schwicke/hexapod-robi/media/20210815_222941.jpg

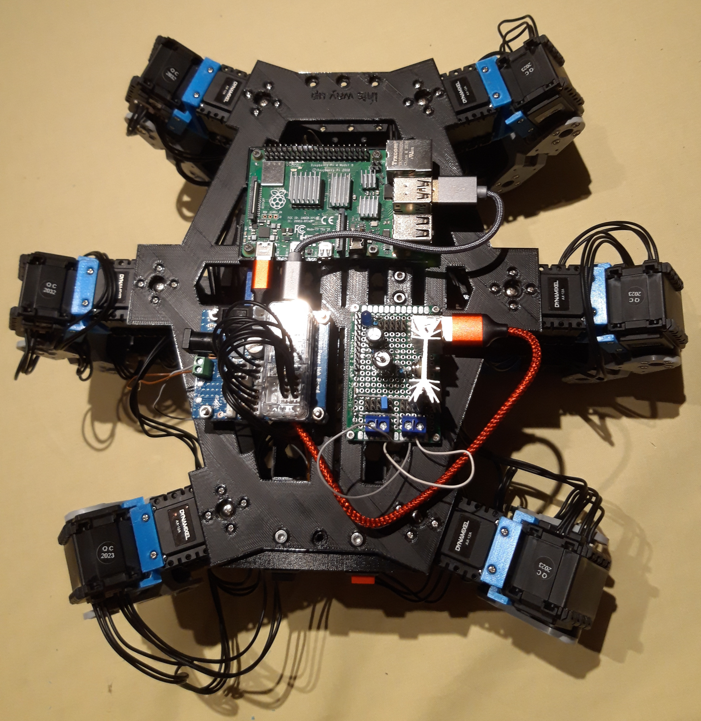
media/20210815_222941.jpg
