schwicke/hexapod-robi/hardware/scad/body/bodymiddle.scad

//
// This file is part of the hexapod-robi distribution (https://github.com/schwicke/hexapod-robi).
// Copyright (c) 2021 Ulrich Schwickerath
//
// This program is free software: you can redistribute it and/or modify
// it under the terms of the GNU General Public License as published by
// the Free Software Foundation, version 3.
//
// This program is distributed in the hope that it will be useful, but
// WITHOUT ANY WARRANTY; without even the implied warranty of
// MERCHANTABILITY or FITNESS FOR A PARTICULAR PURPOSE. See the GNU
// General Public License for more details.
//
// You should have received a copy of the GNU General Public License
// along with this program. If not, see <http://www.gnu.org/licenses/>.
//
// This is a little plastic bit which is intended to get the holes for the connectors
// at the right position. It's not part of the robot itself, but useful for building it.
//

include <../lib/globals.scad>
include <../lib/nuts_and_screws.scad>
include <../lib/mounts.scad>
include <../lib/bodyhelpers.scad>

// global parameters
top_size_scaler = 0.8;

// electronics
power_pos_x = 25;
power_pos_y = 58;
power_spacer_height = 3;
power_converter_scale = 0.7;
//
pcb_hole_dist = 2.0;
pcb_spacer_height = 3;
pcb_x_size = 40;
pcb_y_size = 60;

// disk
delta = 0.2;
ssd_x = 75.0 + delta;
ssd_y = 57.0 + delta;
ssd_z = 11.0 + delta;
ssd_pos_x = 0;
ssd_pos_y = -50;
ssd_height = ssd_z + thickness;
module pcb_spacers(x, y, d, mode){
     // spacers
     translate([-power_pos_x, power_pos_y, 0]){
          translate([ x/2-pcb_hole_dist,  y/2-pcb_hole_dist, 0])spacer_mX(d, pcb_spacer_height);
          translate([ x/2-pcb_hole_dist, -y/2+pcb_hole_dist, 0])spacer_mX(d, pcb_spacer_height);
          translate([-x/2+pcb_hole_dist,  y/2-pcb_hole_dist, 0])spacer_mX(d, pcb_spacer_height);
          translate([-x/2+pcb_hole_dist, -y/2+pcb_hole_dist, 0])spacer_mX(d, pcb_spacer_height);
     }
}

module pcb_holes(x, y, d, mode){
     translate([-power_pos_x, power_pos_y, 0]){
          translate([ x/2-pcb_hole_dist,  y/2-pcb_hole_dist, 0])if (mode==0) my_screwhole_mX(d); else nuthole_mX(d);
          translate([ x/2-pcb_hole_dist, -y/2+pcb_hole_dist, 0])if (mode==0) my_screwhole_mX(d); else nuthole_mX(d);
          translate([-x/2+pcb_hole_dist,  y/2-pcb_hole_dist, 0])if (mode==0) my_screwhole_mX(d); else nuthole_mX(d);
          translate([-x/2+pcb_hole_dist, -y/2+pcb_hole_dist, 0])if (mode==0) my_screwhole_mX(d); else nuthole_mX(d);
     }
}

module power_spacers(scale, d, mode){
  // add spacers
  translate([power_pos_x, power_pos_y, 0]){
    translate([ 24*scale, 21*scale, 0])spacer_mX(d, power_spacer_height);
    translate([-24*scale, 21*scale, 0])spacer_mX(d, power_spacer_height);
    translate([ 24*scale,-21*scale, 0])spacer_mX(d, power_spacer_height);
    translate([-24*scale,-21*scale, 0])spacer_mX(d, power_spacer_height);
  }
}

module power_holes(scale, d, mode){
  translate([power_pos_x, power_pos_y, 0])
    union(){
    translate([ 24*scale, 21*scale, 0]) rotate([0,180,0]) if (mode==0) my_screwhole_mX(d); else nuthole_mX(d);
    translate([-24*scale, 21*scale, 0]) rotate([0,180,0]) if (mode==0) my_screwhole_mX(d); else nuthole_mX(d);
    translate([ 24*scale,-21*scale, 0]) rotate([0,180,0]) if (mode==0) my_screwhole_mX(d); else nuthole_mX(d);
    translate([-24*scale,-21*scale, 0]) rotate([0,180,0]) if (mode==0) my_screwhole_mX(d); else nuthole_mX(d);
  }
}

module ssd_frame(){
     difference(){
          cube([ssd_x+thickness+0.1, ssd_y+thickness+0.1, ssd_height], center=true);
          translate([0, 0, thickness])cube([ssd_x, ssd_y, ssd_height], center=true);
          translate([ssd_x/2, 0, thickness])cube([40, 40, ssd_height], center=true);
          translate([-ssd_x/2, 0, thickness])cube([40, 40, ssd_height], center=true);
     }
}

module mount(){
  //translate([0., 0., space/2  ])cube([10, 20, space+thickness/2], center=true);
  wx = 4*raster+raster/2;
  wy = 8*raster+raster/2;
  wyp = (wy-m3s_nut_width)/4.0;
  difference(){
    union(){
      mount_plate();
      translate([-wx/2, -wy, -thickness/2])cube([wx, 2*wy-5, thickness]);
      translate([0,  15, 0])cube([125, 10, thickness], center=true);
    }
    // screw holes to mount on previous layer
    translate([0, 0, 0-1])rotate([180, 0, 0])mount_holes();
  }
}

// create the body part
module bodymiddle(){
  xleg = 40*0.95;  // position outer legs in x
  yleg = 110*0.9;  // position outer legs in y
  wleg = 20;       // Angle of the outer legs
  difference(){
    union(){
      difference(){
        scale([0.9,1.,1.]){
          linear_extrude(height=thickness, center=true, convexity=0, twist=0, slices=10, scale=1.0){
            resize([180, 230])circle(d=10, $fn=6);
          }
        }
        scale([0.9*top_size_scaler,0.95*top_size_scaler,1.]){
            linear_extrude(height=thickness+3, center=true, convexity=0, twist=0, slices=10, scale=1.0){
            resize([180, 230])circle(d=10, $fn=6);
          }
        }
      anchors_carveout(xleg, yleg, wleg);
      }
      // add the motor anchors
      anchors(xleg, yleg, wleg, thickness);
      // add text
      translate([-18, -103, thickness/2])scale([0.5, 0.5, 1.0])linear_extrude(height=1, center=true, convexity=0, twist=0, slices=10, scale=1.0)text("this way up");
    }
    // add some screwholes
    translate([0, -110, 1])my_screwhole_mX(3);
    translate([16, -110, 1])my_screwhole_mX(3);
    translate([-16, -110, 1])my_screwhole_mX(3);
    translate([0, 110, 1])my_screwhole_mX(3);
    translate([16, 110, 1])my_screwhole_mX(3);
    translate([-16, 110, 1])my_screwhole_mX(3);
  }
  // mount connectors
  translate([-base_mount_pos_x, 0, 0])mount();
  translate([+base_mount_pos_x, 0, 0])mount();
  // supports and spacers for u2d2 and power converters
  pcb_spacers(pcb_x_size, pcb_y_size, 2.5, 1);
  power_spacers(1, 3, 0);
}

difference(){
  union(){
    bodymiddle();
    translate([0, -20, 0])cube([120, 10, thickness], center=true);
    translate([0, 25, 0])cube([120, 10, thickness], center=true);
    translate([2*power_pos_x-1.5, power_pos_y, 0.0])cube([8, 60, thickness], center=true);
    translate([0.5, 0, 0.0])cube([10, 60, thickness], center=true);
    translate([0, 60, 0.0])cube([40, 70, thickness], center=true);
    translate([-pcb_x_size-6, power_pos_y-7, 0.0])cube([18, 50, thickness], center=true);
    translate([ssd_pos_x, ssd_pos_y, ssd_height/2-thickness/2])ssd_frame();
  }
  // drill holes for screws through all of it
  pcb_holes(pcb_x_size, pcb_y_size, 2.5, 1);
  power_holes(1, 3, 0);
  etages(180);
}
