schwicke/hexapod-robi/software/python/hexapod_config.py

#
# This file is part of the hexapod-robi distribution (https://github.com/schwicke/hexapod-robi).
# Copyright (c) 2021 Ulrich Schwickerath
#
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

spider_config = {
    "controllers": {
        "u2d2_1":{
            'port': '/dev/ttyUSB0',
            'sync_read': False,
            'attached_motors': ['leg1', 'leg2', 'leg3', 'leg4', 'leg5', 'leg6'],
            'protocol': 1
        }
    },
    "motors": {
        "motor_1": {
            "id": 1,
            "type": "AX-12",
            "offset": 0.0,
            "orientation": "direct",
            "angle_limit": [
                -150,
                150
            ]
        },
        "motor_2": {
            "id": 2,
            "type": "AX-12",
            "offset": 0.0,
            "orientation": "direct",
            "angle_limit": [
                -150,
                150
            ]
        },
        "motor_3": {
            "id": 3,
            "type": "AX-12",
            "offset": 0.0,
            "orientation": "direct",
            "angle_limit": [
                -150,
                150
            ]
        },
        "motor_4": {
            "id": 4,
            "type": "AX-12",
            "offset": 0.0,
            "orientation": "direct",
            "angle_limit": [
                -150,
                150
            ]
        },
        "motor_5": {
            "id": 5,
            "type": "AX-12",
            "offset": 0.0,
            "orientation": "direct",
            "angle_limit": [
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
        'leg2': ['motor_4', 'motor_5', 'motor_6'],
        'leg3': ['motor_7', 'motor_8', 'motor_9'],
        'leg4': ['motor_10', 'motor_11', 'motor_12'],
        'leg5': ['motor_13', 'motor_14', 'motor_15'],
        'leg6': ['motor_16', 'motor_17', 'motor_18']
    }
}
