schwicke/hexapod-robi/hardware/electronics/sensors/tests/src/hc-sr04.c

/*
This file is part of the hexapod-robi distribution (https://github.com/schwicke/hexapod-robi).
Copyright (c) 2021 Ulrich Schwickerath

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
You should have received a copy of the GNU General Public License
along with this program. If not, see <http://www.gnu.org/licenses/>.
*/
#include <gpiod.h>
#include <stdio.h>
#include <unistd.h>
#include <sys/time.h>
#include "hc-sr04.h"

void init_hardware()
{
  openChip();
  trig1Line  = setAsOutput(trig1Pin);
  echo1Line  = setAsInput(echo1Pin);
  trig2Line  = setAsOutput(trig2Pin);
  echo2Line  = setAsInput(echo2Pin);
}

float getDistance(struct gpiod_line * trigLine, struct gpiod_line * echoLine){
  struct timeval t0, tb, te;
  long micros;
  float distance;

  micros = 0;
  gettimeofday(&t0, NULL);
  gettimeofday(&tb, NULL);
  gettimeofday(&te, NULL);
  writeState(trigLine, HIGH); //send 10us high level to trigPin
  delayMicroseconds(10);
  writeState(trigLine, LOW);
  micros = 0;
  while (readState(echoLine) == 0)
    {
      gettimeofday(&tb, NULL);
      if ((tb.tv_sec-t0.tv_sec) > 1)
        {
          return -1;
        }
    };
  while (readState(echoLine) )
    {
      gettimeofday(&te, NULL);
      if ((te.tv_sec-t0.tv_sec) > 1)
        {
          return -1;
        }
    };
  micros = te.tv_usec-tb.tv_usec;
  distance = (float)micros/10000.0 * 343.0 / 2.0 ; //calculate distance with sound speed 340m/s
  return distance;
}

int main(){
  init_hardware();
  writeState(trig1Line, LOW);
  writeState(trig2Line, LOW);

  float distance_front = 0.0;
  float distance_rear = 0.0;
  while(1){
    distance_front = getDistance(trig1Line, echo1Line);
    distance_rear = getDistance(trig2Line, echo2Line);
    printf("The distances are : %.2f cm and %.2f cm\n", distance_front, distance_rear);
    delay(1000);
  }
}
